CyberZeroHun/Mobil_Beagyazott_Projekt/junk/tár3.png

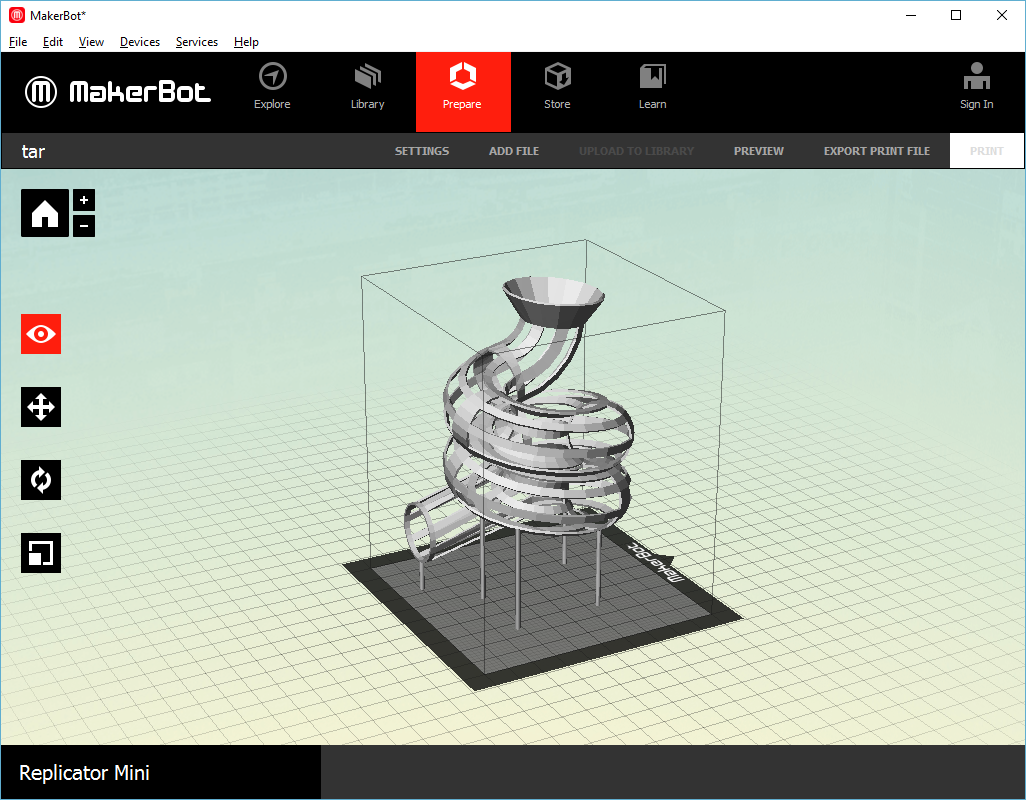
junk/tár3.png
