CyberZeroHun/Mobil_Beagyazott_Projekt/img/servo.png

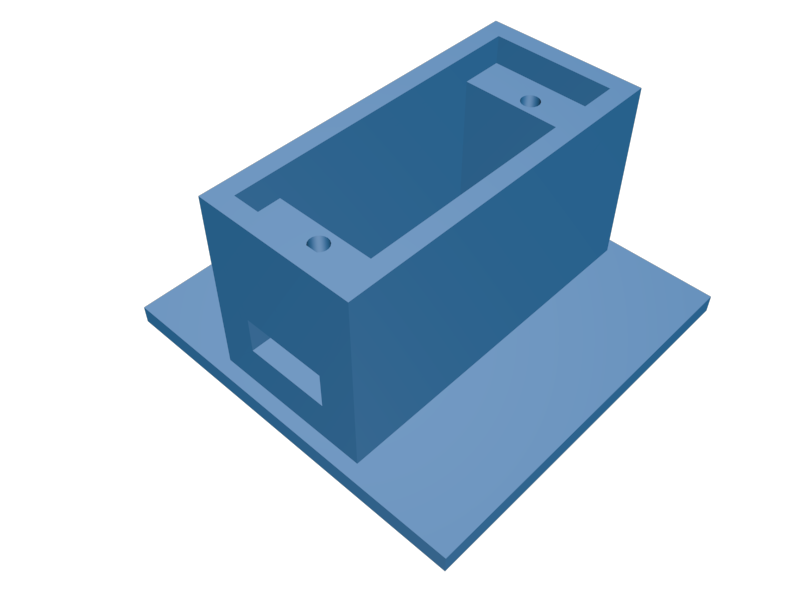
img/servo.png
