CyberZeroHun/Mobil_Beagyazott_Projekt/img/ultrahang4.png

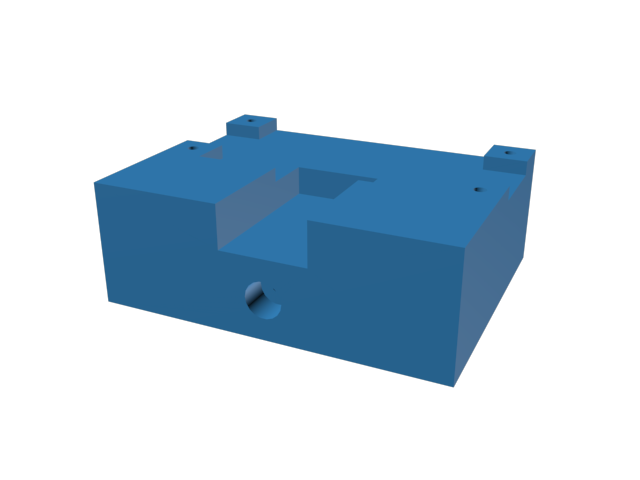
img/ultrahang4.png
