CyberZeroHun/Mobil_Beagyazott_Projekt/junk/kameratarto.png

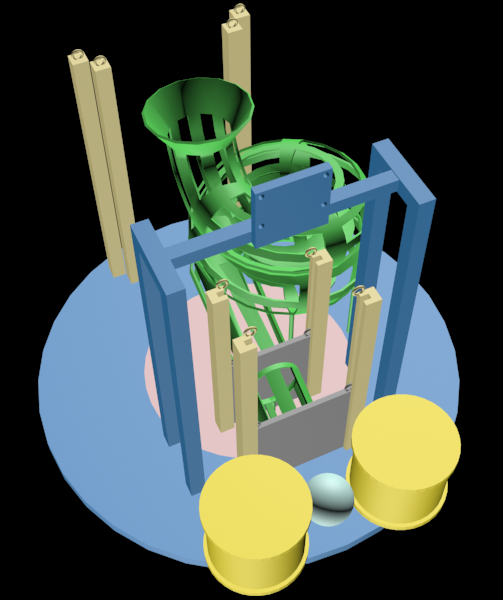
junk/kameratarto.png
