CyberZeroHun/Mobil_Beagyazott_Projekt/junk/kapuk1.png

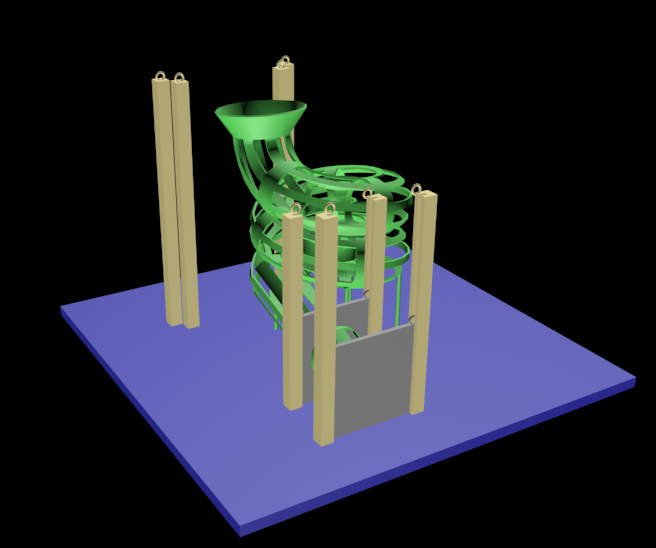
junk/kapuk1.png
