CyberZeroHun/Mobil_Beagyazott_Projekt/junk/kapuk2_dugdosos.png

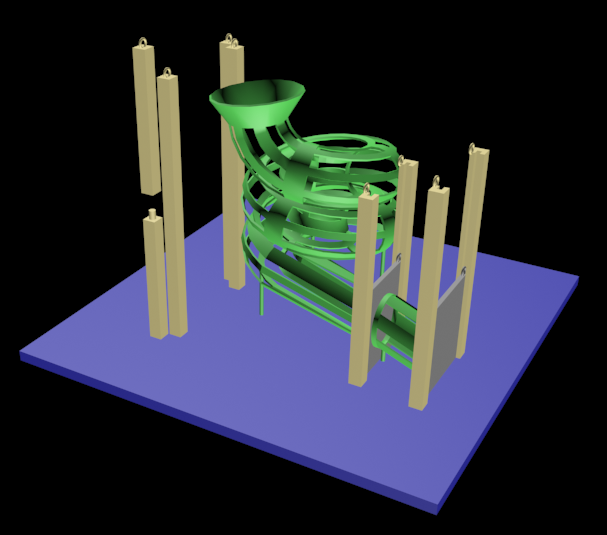
junk/kapuk2_dugdosos.png
