CyberZeroHun/Mobil_Beagyazott_Projekt/junk/seged_objektum1.png

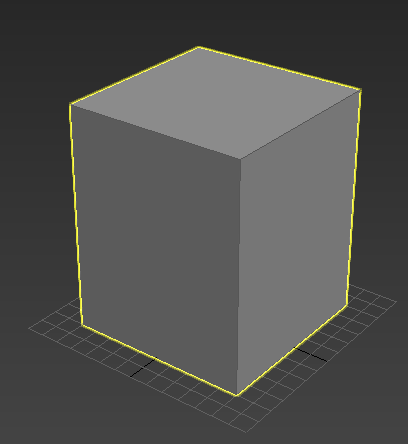
junk/seged_objektum1.png
