CyberZeroHun/Mobil_Beagyazott_Projekt/junk/seged_objektum2.png

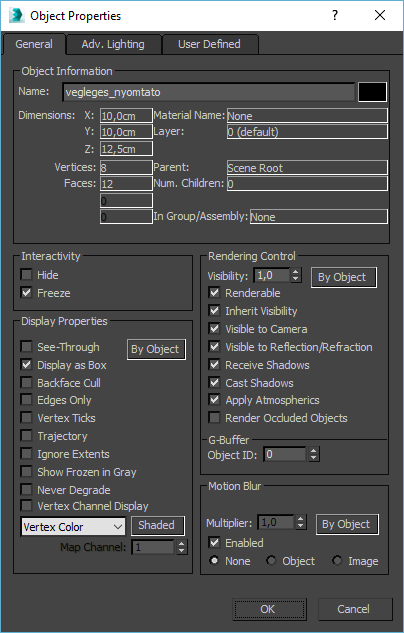
junk/seged_objektum2.png
