CyberZeroHun/Mobil_Beagyazott_Projekt/junk/seged_objektum3.png

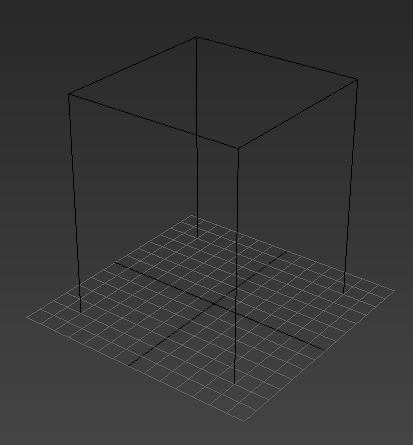
junk/seged_objektum3.png
