CyberZeroHun/Mobil_Beagyazott_Projekt/junk/tár2.png

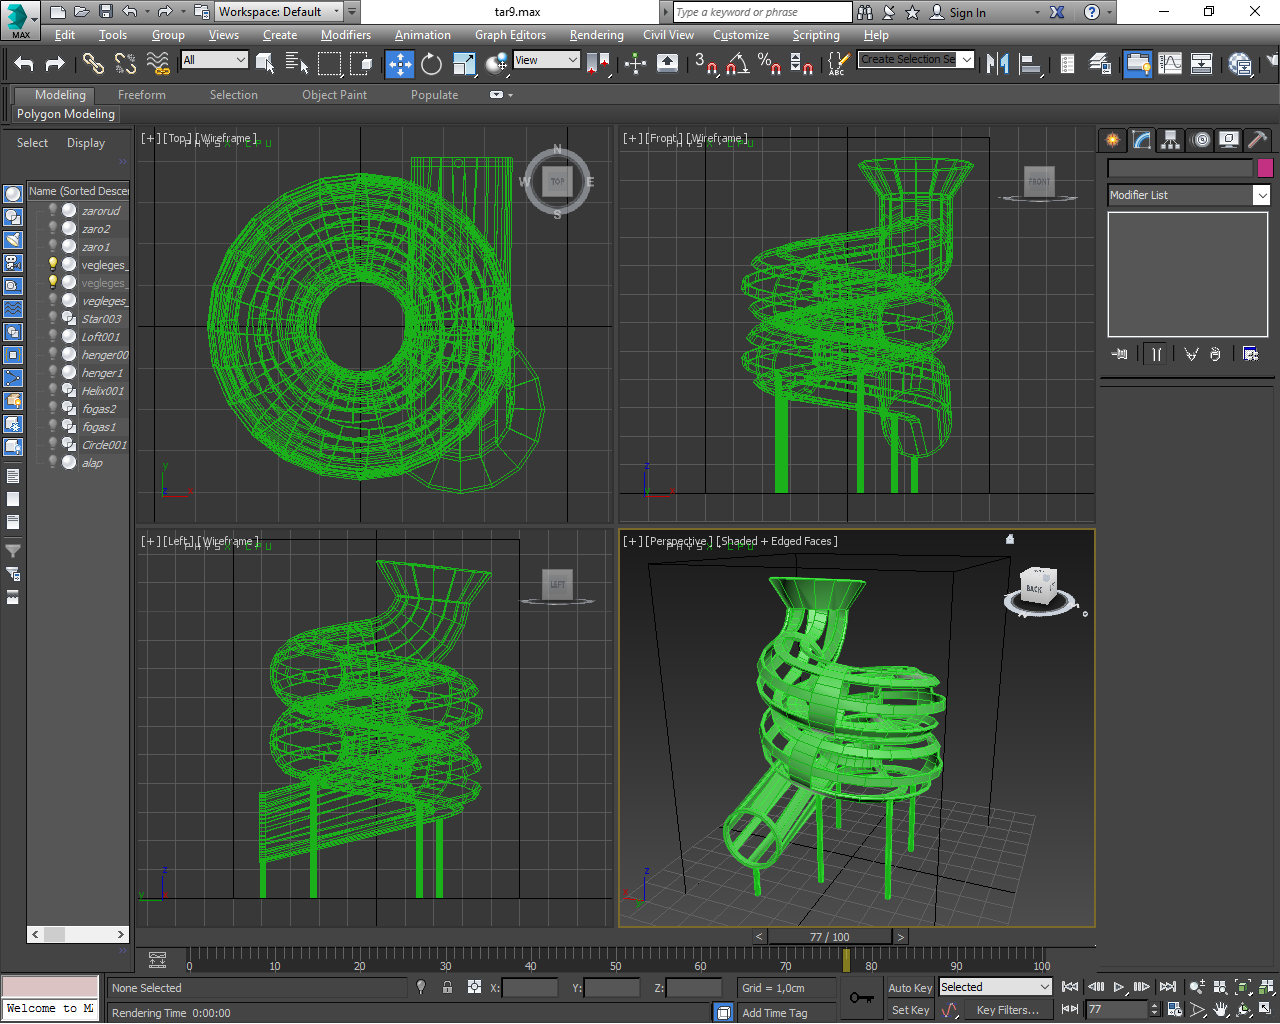
junk/tár2.png
