CyberZeroHun/Mobil_Beagyazott_Projekt/junk/tár4.png

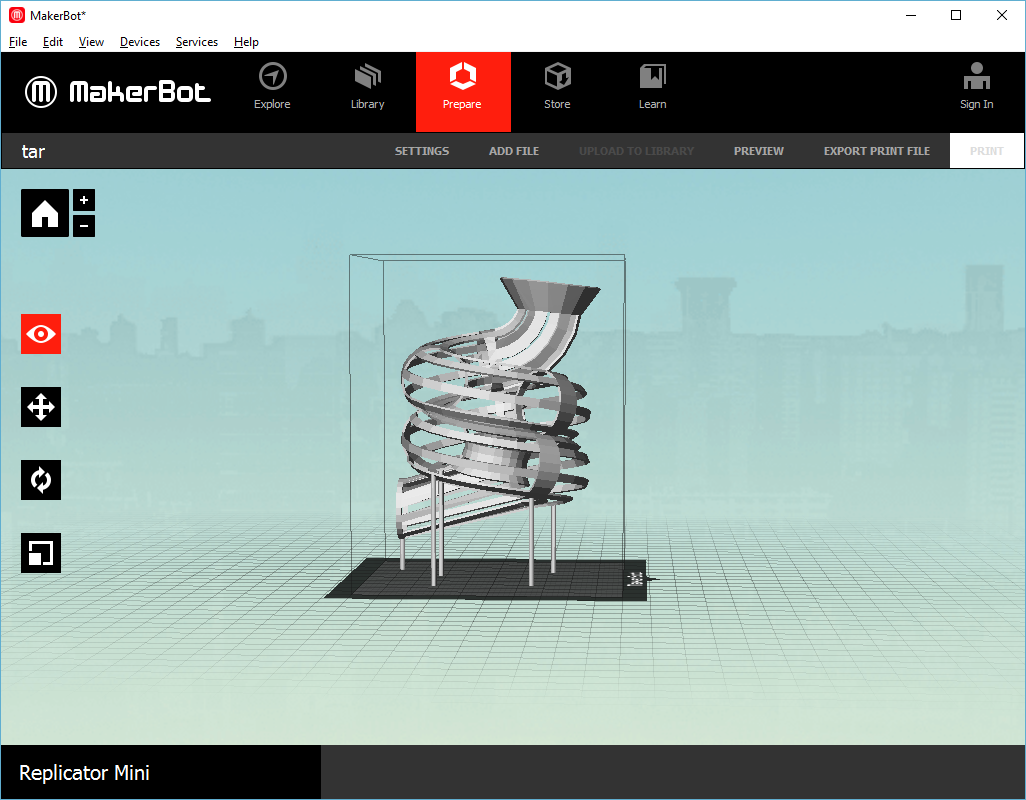
junk/tár4.png
