CyberZeroHun/Mobil_Beagyazott_Projekt/junk/tár5_005.png

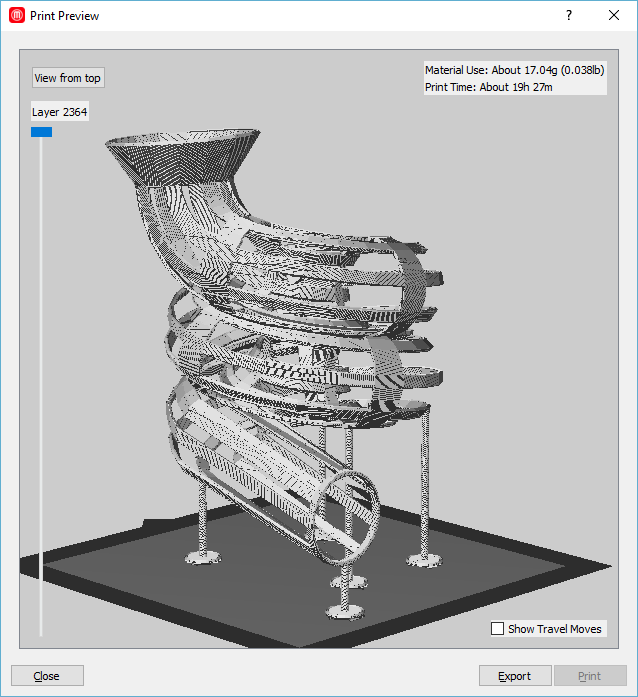
junk/tár5_005.png
