CyberZeroHun/Mobil_Beagyazott_Projekt/junk/tár6_020.png

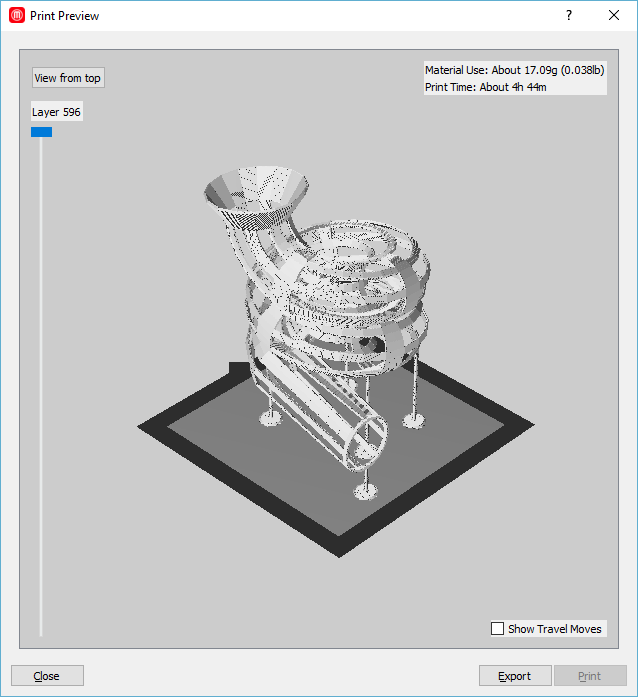
junk/tár6_020.png
