CyberZeroHun/Mobil_Beagyazott_Projekt/junk/tár.png

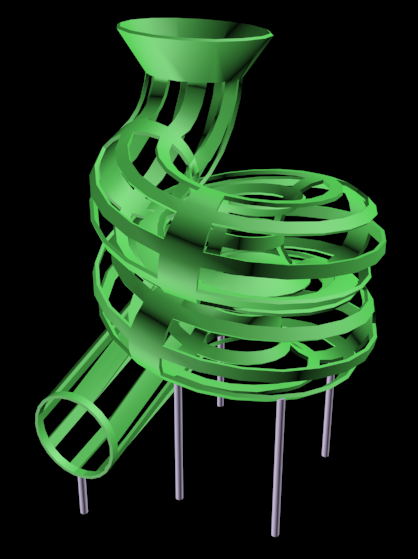
junk/tár.png
