CyberZeroHun/Mobil_Beagyazott_Projekt/junk/ultrahang2.png

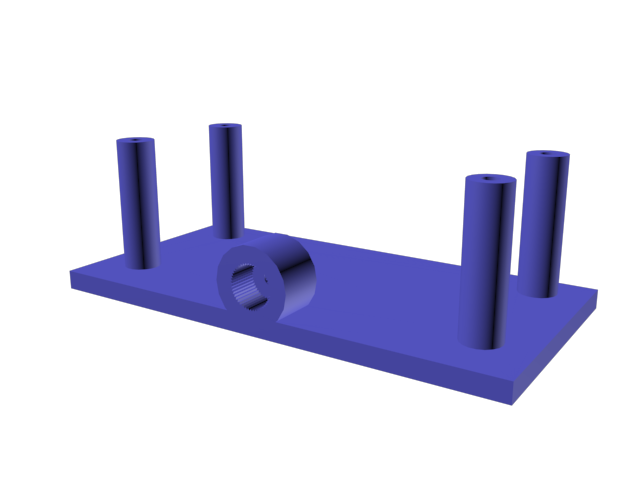
junk/ultrahang2.png
