CyberZeroHun/Mobil_Beagyazott_Projekt/junk/ultrahang_terv.png

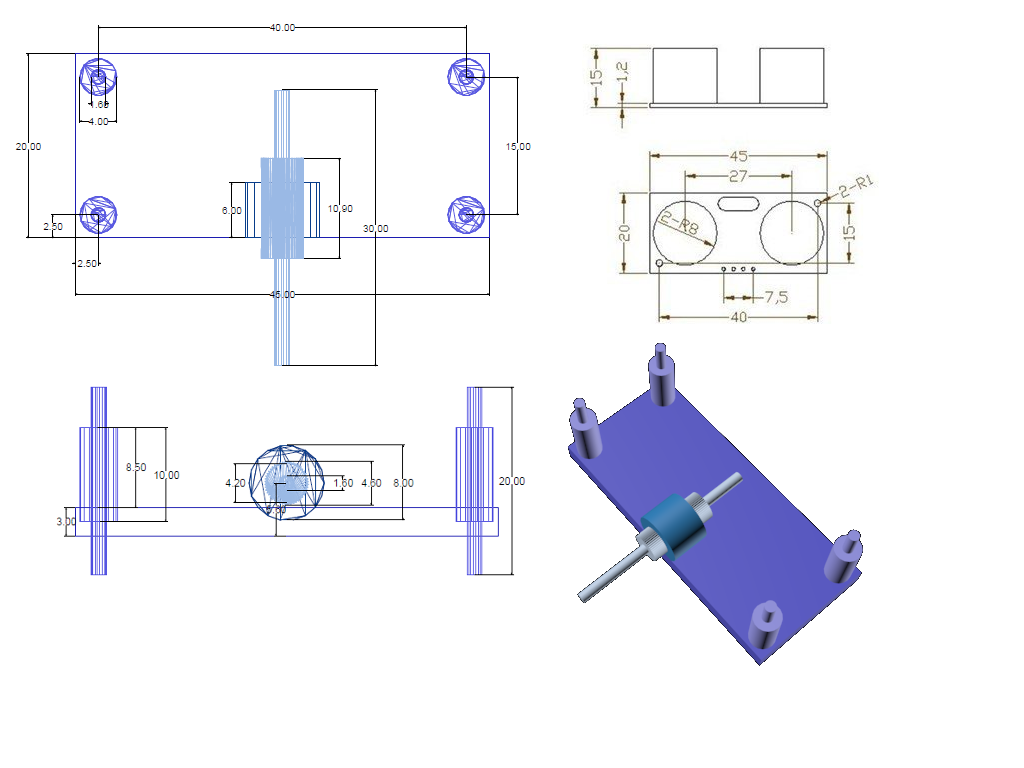
junk/ultrahang_terv.png
