CyberZeroHun/Mobil_Beagyazott_Projekt/junk/unit_1.png

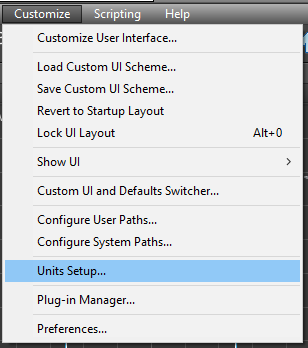
junk/unit_1.png
