CyberZeroHun/Mobil_Beagyazott_Projekt/junk/unit_2.png

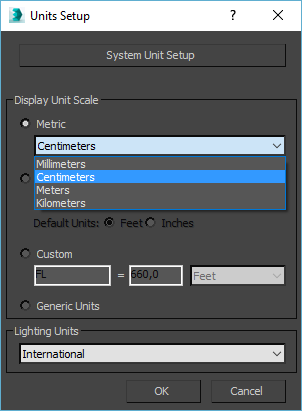
junk/unit_2.png
