CyberZeroHun/Mobil_Beagyazott_Projekt/junk/unit_3.png

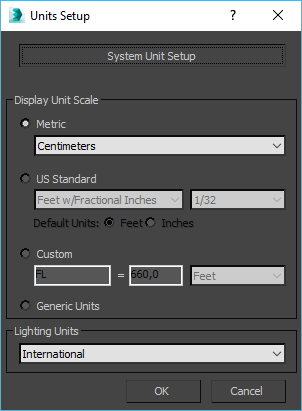
junk/unit_3.png
