CyberZeroHun/Mobil_Beagyazott_Projekt/junk/unit_4.png

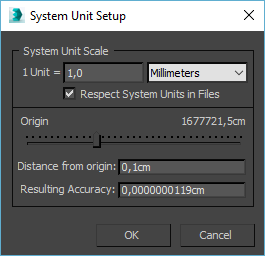
junk/unit_4.png
