CyberZeroHun/Mobil_Beagyazott_Projekt/junk/unit_5.png

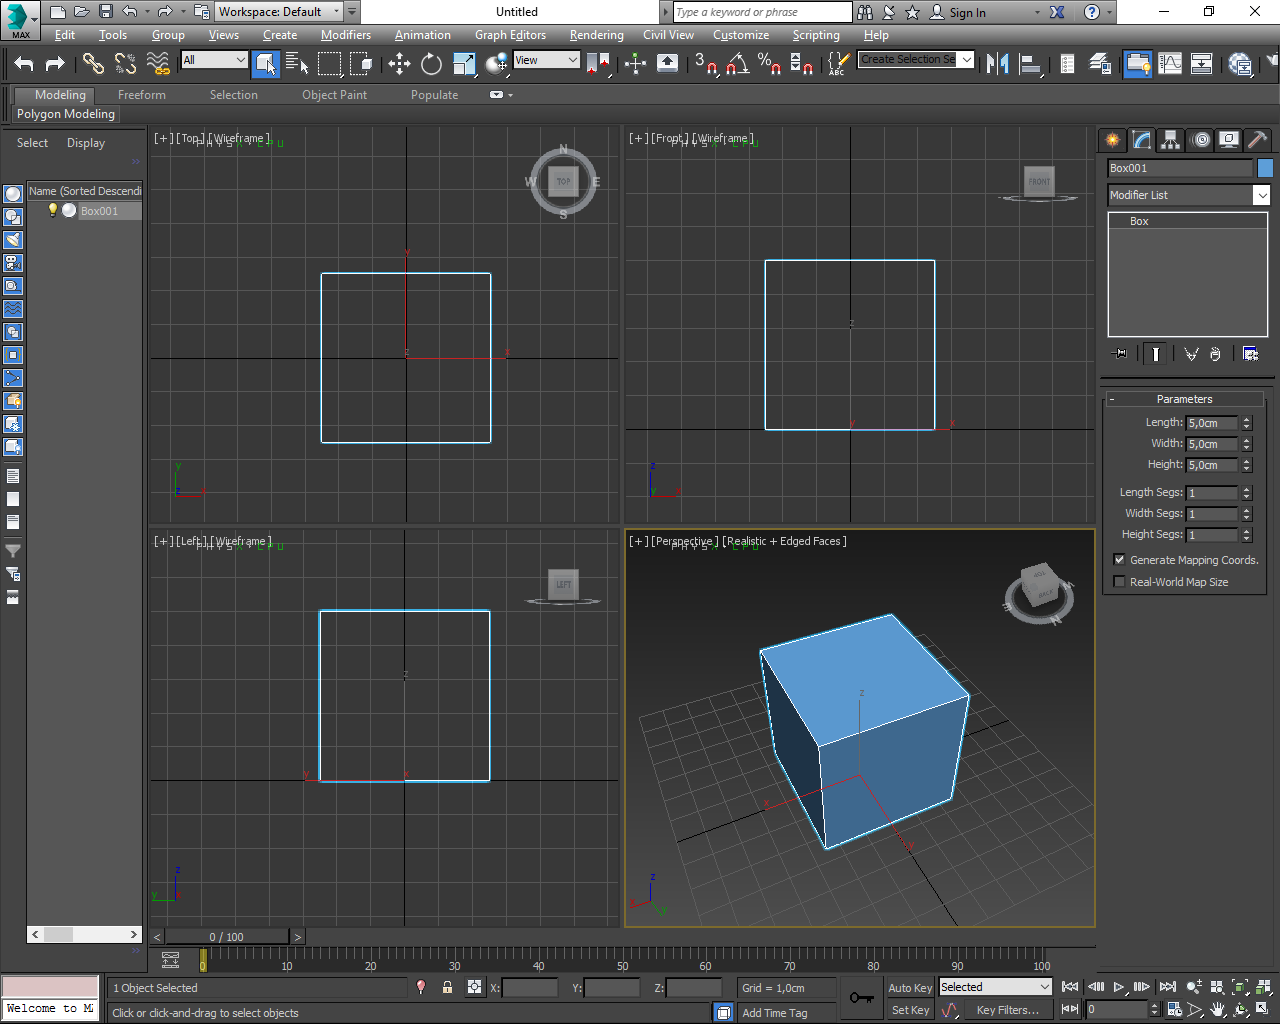
junk/unit_5.png
