CyberZeroHun/Mobil_Beagyazott_Projekt/junk/unit_6b.png

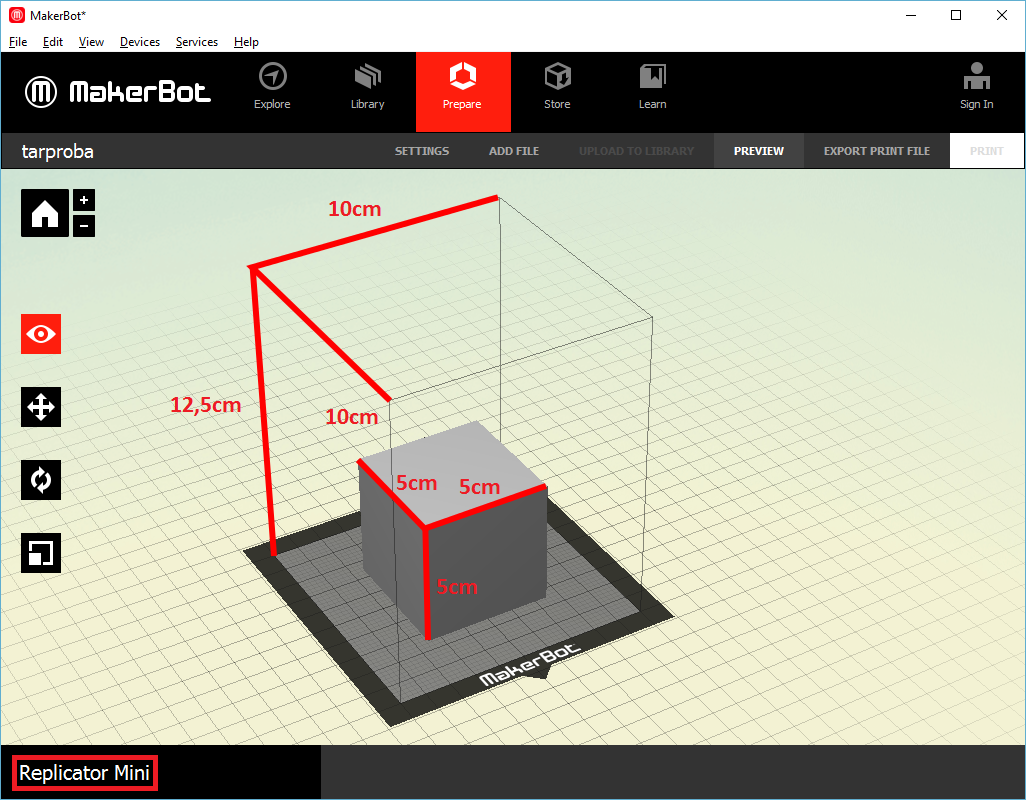
junk/unit_6b.png
