CyberZeroHun/Mobil_Beagyazott_Projekt/junk/print_export2.png

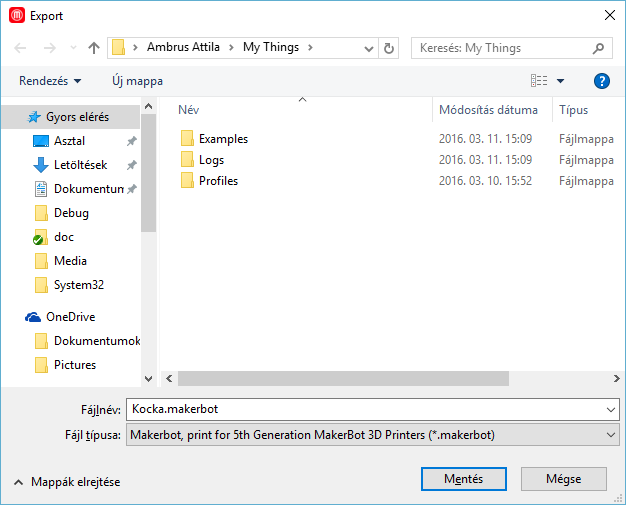
junk/print_export2.png
