CyberZeroHun/Mobil_Beagyazott_Projekt/junk/print_preview3.png

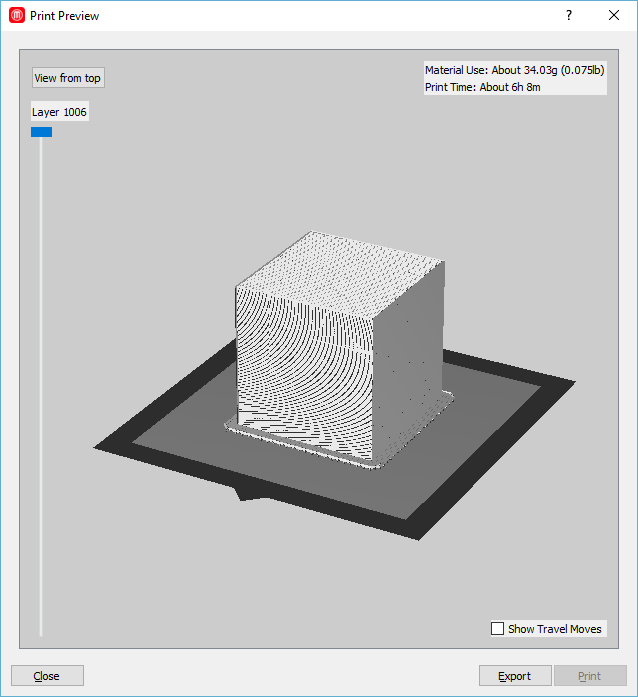
junk/print_preview3.png
