CyberZeroHun/Mobil_Beagyazott_Projekt/junk/print_preview4.png

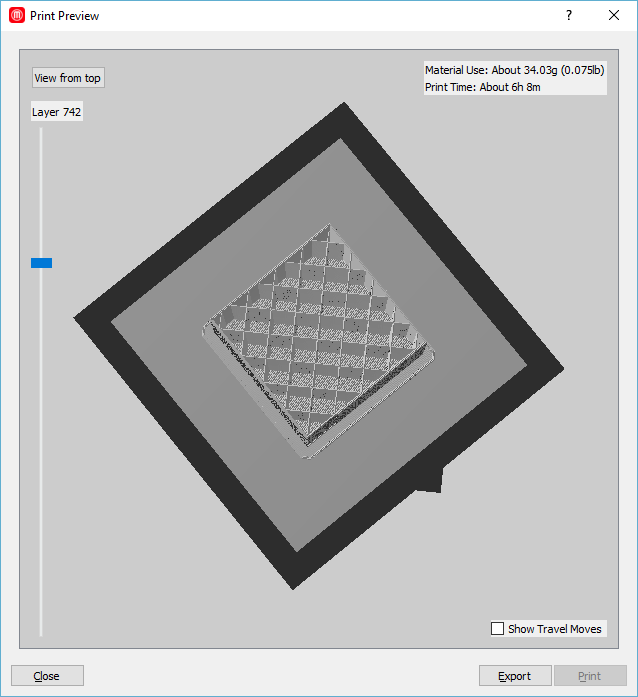
junk/print_preview4.png
