CyberZeroHun/Mobil_Beagyazott_Projekt/junk/print_preview5b.png

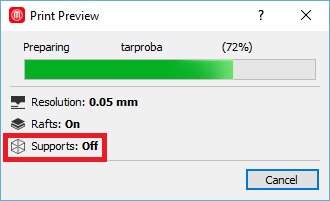
junk/print_preview5b.png
