CyberZeroHun/Mobil_Beagyazott_Projekt/junk/print_setting3.png

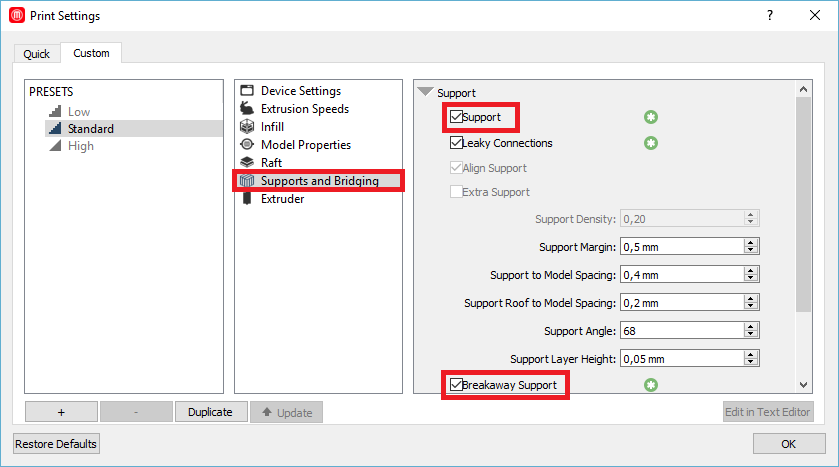
junk/print_setting3.png
