CyberZeroHun/Mobil_Beagyazott_Projekt/junk/print_setting4.png

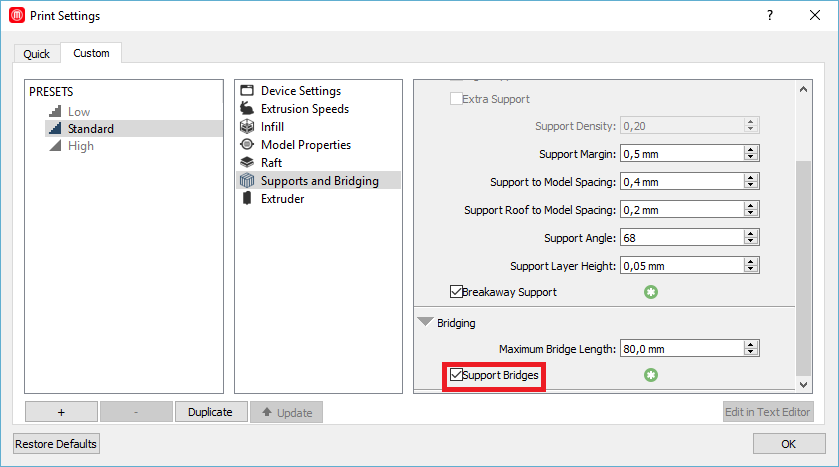
junk/print_setting4.png
